rcjcooke/weltec-snake/electronics/schematic.sch

## EAGLE design electronics/schematic.sch (2018-11-03)

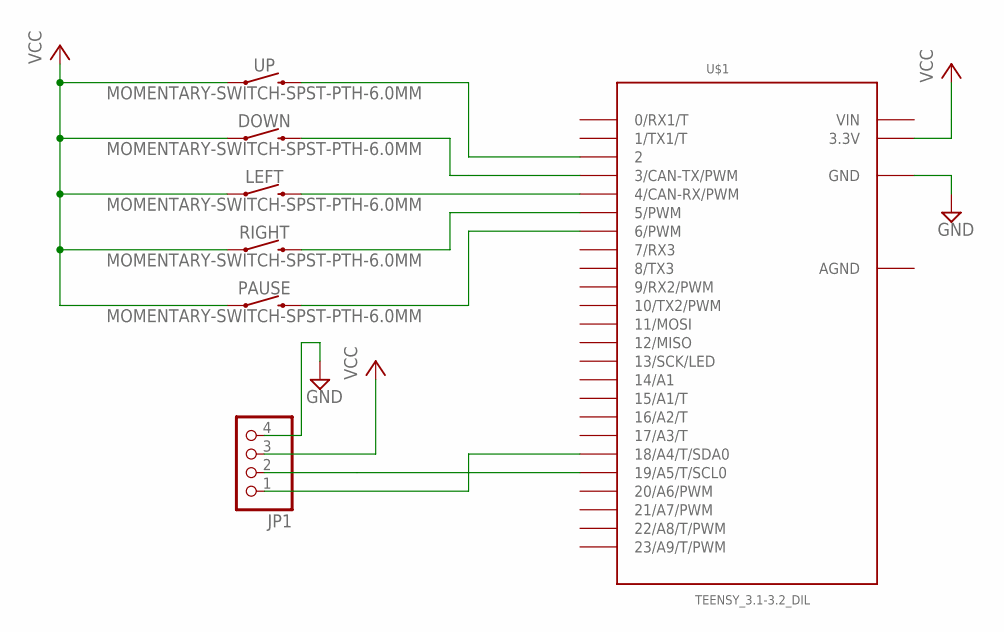
[picture p9: schematic schematic.sch]

Parts:
DOWN: MOMENTARY-SWITCH-SPST-PTH-6.0MM; TACTILE_SWITCH_PTH_6.0MM
JP1: PINHD-1X4; 1X04
LEFT: MOMENTARY-SWITCH-SPST-PTH-6.0MM; TACTILE_SWITCH_PTH_6.0MM
PAUSE: MOMENTARY-SWITCH-SPST-PTH-6.0MM; TACTILE_SWITCH_PTH_6.0MM
RIGHT: MOMENTARY-SWITCH-SPST-PTH-6.0MM; TACTILE_SWITCH_PTH_6.0MM
U$1: TEENSY_3.1-3.2_DIL; TEENSY_3.0-3.2&LC_DIL
UP: MOMENTARY-SWITCH-SPST-PTH-6.0MM; TACTILE_SWITCH_PTH_6.0MM

Connections:
GND: JP1.4, U$1.GND
unnamed: JP1.2, U$1.19/A5 (19/A5/T/SCL0)
unnamed: U$1.2, UP.3 (2)
unnamed: JP1.1, U$1.18/A4 (18/A4/T/SDA0)
unnamed: DOWN.3 (2), U$1.3 (3/CAN-TX/PWM)
unnamed: LEFT.3 (2), U$1.4 (4/CAN-RX/PWM)
unnamed: RIGHT.3 (2), U$1.5 (5/PWM)
unnamed: PAUSE.3 (2), U$1.6 (6/PWM)
VCC: DOWN.1, JP1.3, LEFT.1, PAUSE.1, RIGHT.1, U$1.3.3V, UP.1
