rcjcooke/weltec-snake/software/src/Images.hpp

#ifndef __IMAGES_H_INCLUDED__
#define __IMAGES_H_INCLUDED__

#include <Arduino.h>

// 'MainMenu', 128x64px
static const unsigned char MAIN_MENU_BMP [] PROGMEM = {
	0x00, 0x00, 0x00, 0x00, 0x00, 0x00, 0x00, 0x00, 0x00, 0x00, 0x00, 0x00, 0x00, 0x00, 0x00, 0x00, 
	0x00, 0x00, 0x00, 0x00, 0x00, 0x00, 0x00, 0x00, 0x00, 0x00, 0x00, 0x00, 0x00, 0x00, 0x00, 0x00, 
	0x00, 0x00, 0x00, 0x00, 0x00, 0x3d, 0xef, 0x00, 0x07, 0xbf, 0xf0, 0x00, 0x00, 0x00, 0x7f, 0xf0, 
	0x00, 0x00, 0x00, 0x00, 0x00, 0x3d, 0xef, 0x00, 0x07, 0xbf, 0xf0, 0x00, 0x00, 0x00, 0x7f, 0xf8, 
	0x00, 0x00, 0x00, 0x00, 0x00, 0x3d, 0xef, 0x00, 0x07, 0xbf, 0xf0, 0x00, 0x00, 0x00, 0x7f, 0xf8, 
	0x00, 0x00, 0x00, 0x00, 0x00, 0x3d, 0xef, 0x07, 0x87, 0xbf, 0xf0, 0xf0, 0x1e, 0x00, 0x7f, 0xfc, 
	0x00, 0x00, 0x00, 0x00, 0x00, 0x3d, 0xef, 0x1f, 0xe7, 0x87, 0x83, 0xfc, 0x7f, 0x00, 0x00, 0x3c, 
	0x00, 0x00, 0x00, 0x00, 0x00, 0x3d, 0xef, 0x1f, 0xe7, 0x87, 0x83, 0xfc, 0x7f, 0x80, 0x03, 0xbc, 
	0x00, 0x00, 0x00, 0x00, 0x00, 0x3d, 0xef, 0x3c, 0xf7, 0x87, 0x87, 0x9e, 0xff, 0x80, 0x03, 0xfc, 
	0x00, 0x00, 0x00, 0x00, 0x00, 0x3d, 0xef, 0x3f, 0xf7, 0x87, 0x87, 0xfe, 0xf0, 0x40, 0x03, 0xfc, 
	0x00, 0x00, 0x00, 0x00, 0x00, 0x3d, 0xef, 0x3f, 0xf7, 0x87, 0x87, 0xfe, 0xf3, 0xc0, 0x01, 0xf8, 
	0x00, 0x00, 0x00, 0x00, 0x00, 0x3f, 0xff, 0x3f, 0x07, 0x87, 0x87, 0xe0, 0xff, 0x80, 0x00, 0xf0, 
	0x00, 0x00, 0x00, 0x00, 0x00, 0x3f, 0xff, 0x1f, 0x07, 0x87, 0x83, 0xe0, 0x7f, 0x80, 0x00, 0x00, 
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
	0x00, 0x00, 0x00, 0x00, 0x00, 0x38, 0x00, 0x00, 0x00, 0x00, 0x00, 0x00, 0x00, 0x00, 0x00, 0x00, 
	0x00, 0x00, 0x00, 0x00, 0x00, 0x38, 0x00, 0x00, 0x00, 0x00, 0x00, 0x00, 0x00, 0x00, 0x00, 0x00, 
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
};


#endif // __IMAGES_H_INCLUDED__
